brailletouch/Brailletouch/Electronica & firmware/celda braille con motor de celular/STL/assembly3 - PiezaBrailleParaMotores17-1.STL

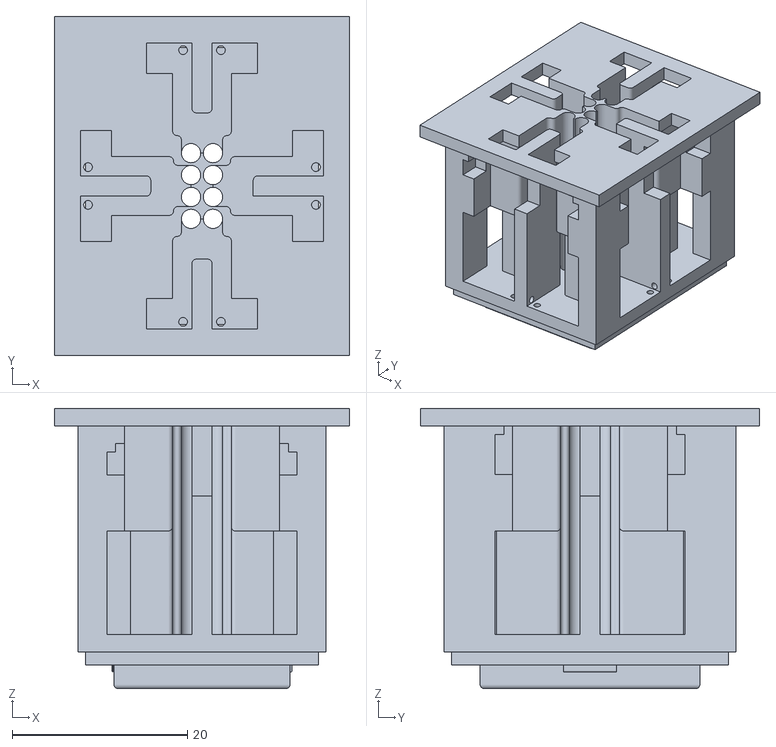
[picture p14: CAD file, 2024-08-29]
Electronica & firmware/celda braille con motor de celular/STL/assembly3 - PiezaBrailleParaMotores17-1.STL
33.7 x 38.7 x 32.0
