brailletouch/Brailletouch/Electronica & firmware/3d files/fcstd/celda completa.FCStd

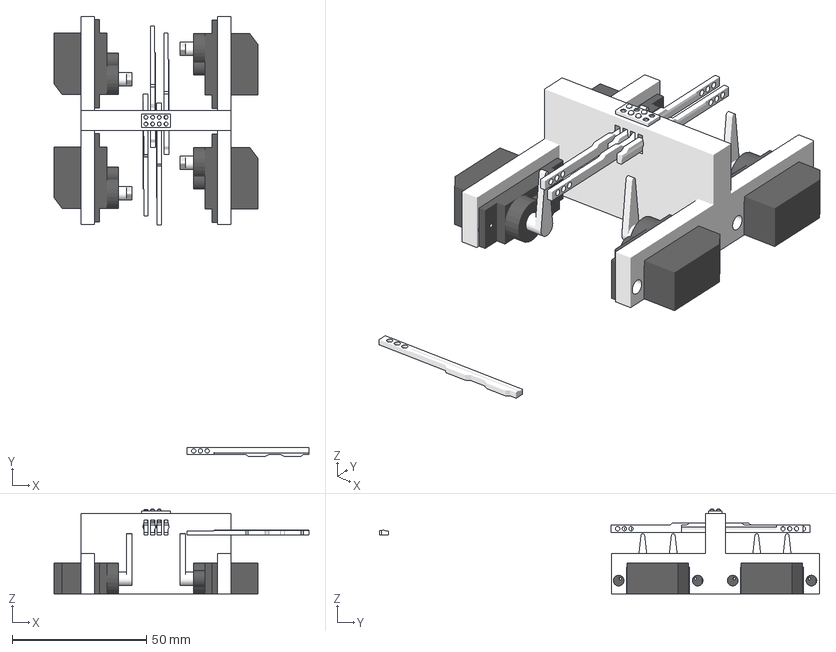
[picture p15: CAD file, 2021-12-04]
Electronica & firmware/3d files/fcstd/celda completa.FCStd
94.9 x 163.9 x 31.7 mm
