brailletouch/Brailletouch/Electronica & firmware/3d files/stl/barilla.stl

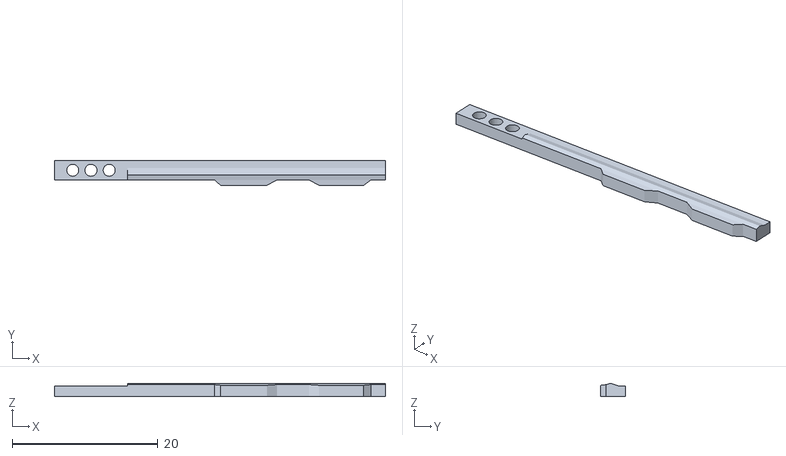
[picture p16: CAD file, 2021-12-04]
Electronica & firmware/3d files/stl/barilla.stl
45.4 x 3.40 x 1.85
