brailletouch/Brailletouch/Electronica & firmware/celda braille con motor de celular/SLDPRT/Pinizquierdo14.SLDPRT

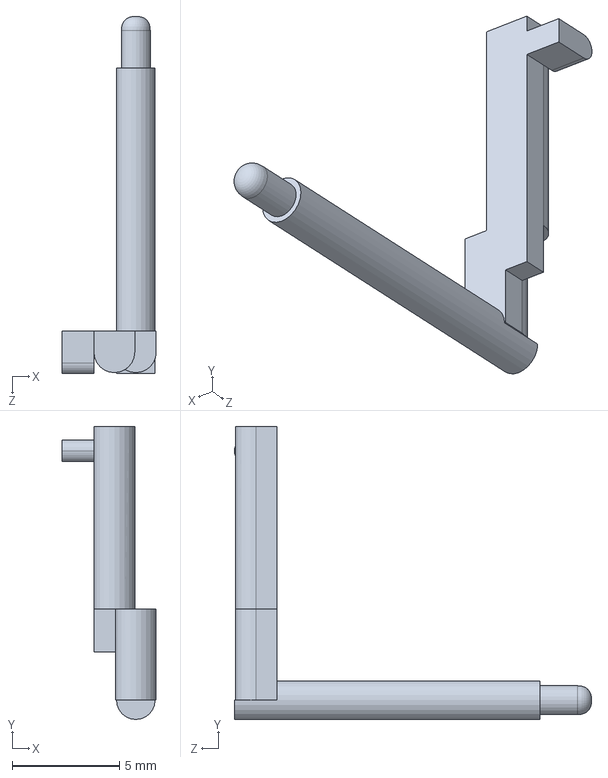
[picture p17: CAD file, 2024-08-17]
Electronica & firmware/celda braille con motor de celular/SLDPRT/Pinizquierdo14.SLDPRT
4.40 x 13.6 x 16.6 mm
