brailletouch/Brailletouch/Electronica & firmware/3d files/stl/celda braille.stl

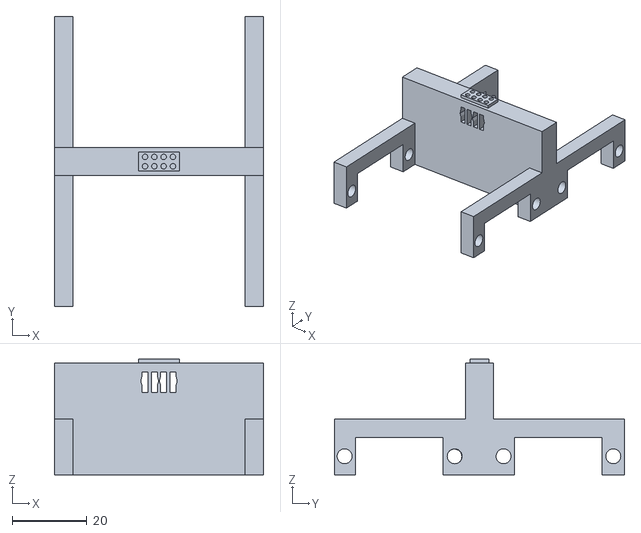
[picture p18: CAD file, 2021-12-04]
Electronica & firmware/3d files/stl/celda braille.stl
55.9 x 77.5 x 31.0
