brailletouch/Brailletouch/Electronica & firmware/celda braille con motor de celular/SLDPRT/TAPA_14.SLDPRT

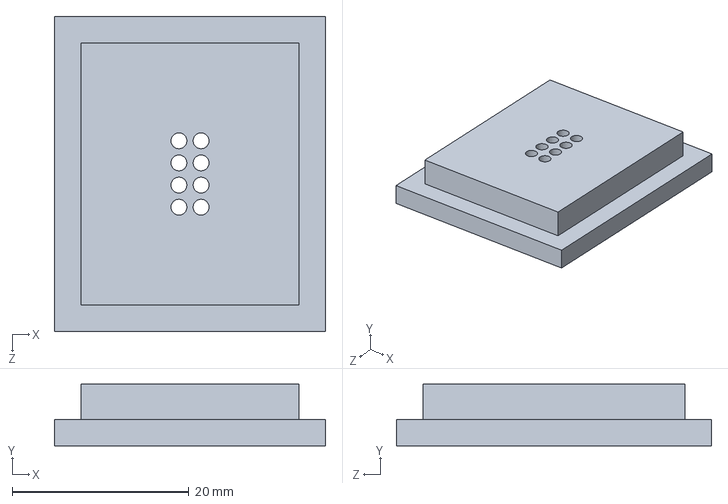
[picture p19: CAD file, 2024-08-17]
Electronica & firmware/celda braille con motor de celular/SLDPRT/TAPA_14.SLDPRT
30.6 x 7.00 x 35.7 mm
