brailletouch/Brailletouch/Electronica & firmware/3d files/stl/punto braille.stl

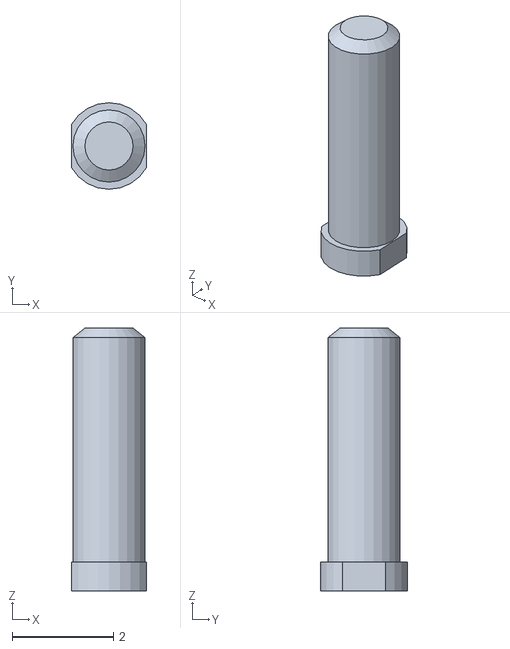
[picture p20: CAD file, 2021-12-04]
Electronica & firmware/3d files/stl/punto braille.stl
1.48 x 1.71 x 5.19
