brailletouch/Brailletouch/Electronica & firmware/celda braille con motor de celular/SLDPRT/PiezaBrailleParaMotores14.SLDPRT

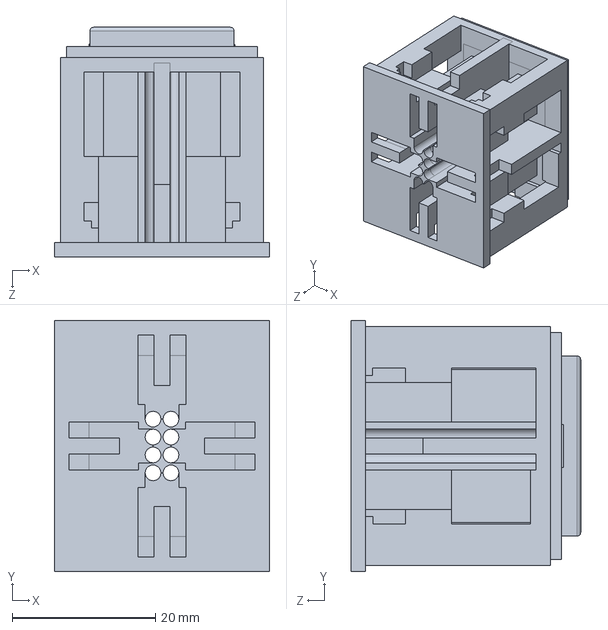
[picture p21: CAD file, 2024-08-17]
Electronica & firmware/celda braille con motor de celular/SLDPRT/PiezaBrailleParaMotores14.SLDPRT
30.0 x 35.0 x 32.0 mm
