brailletouch/Brailletouch/Electronica & firmware/celda braille con motor de celular/SLDPRT/CAPUCHAMOTOR14.SLDPRT

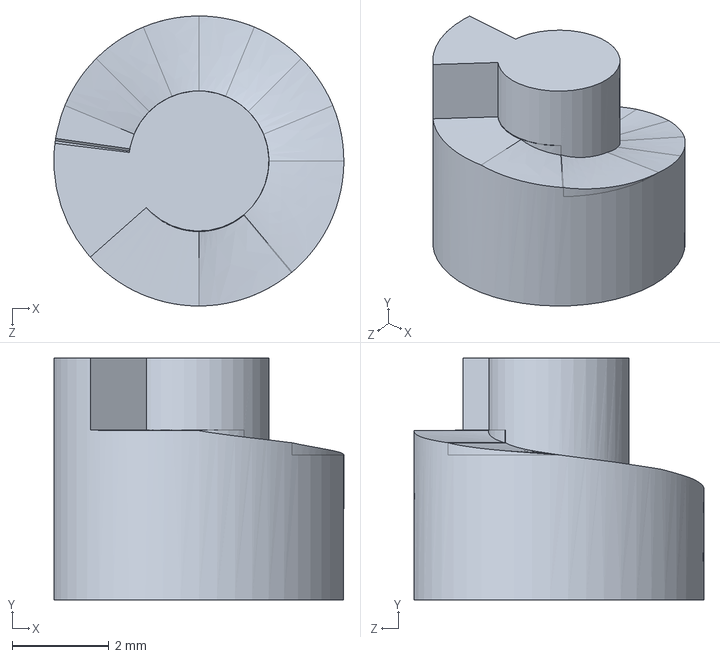
[picture p22: CAD file, 2024-08-17]
Electronica & firmware/celda braille con motor de celular/SLDPRT/CAPUCHAMOTOR14.SLDPRT
5.99 x 5.00 x 6.00 mm
