brailletouch/Brailletouch/Electronica & firmware/celda braille con motor de celular/image/assembly5.PNG

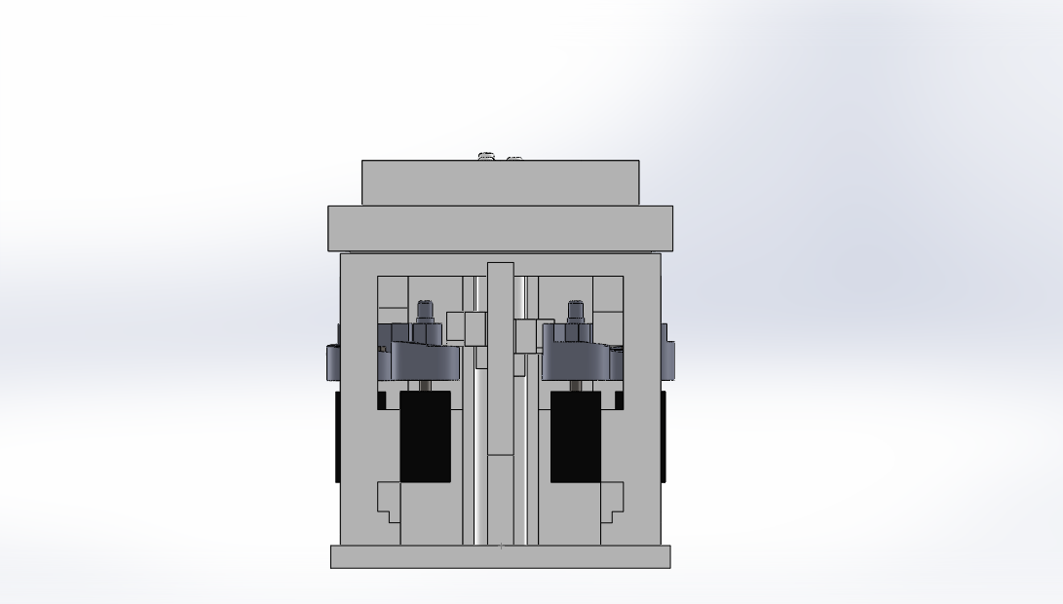
Electronica & firmware/celda braille con motor de celular/image/assembly5.PNG
