brailletouch/Brailletouch/Electronica & firmware/celda braille con motor de celular/image/assembly7.PNG

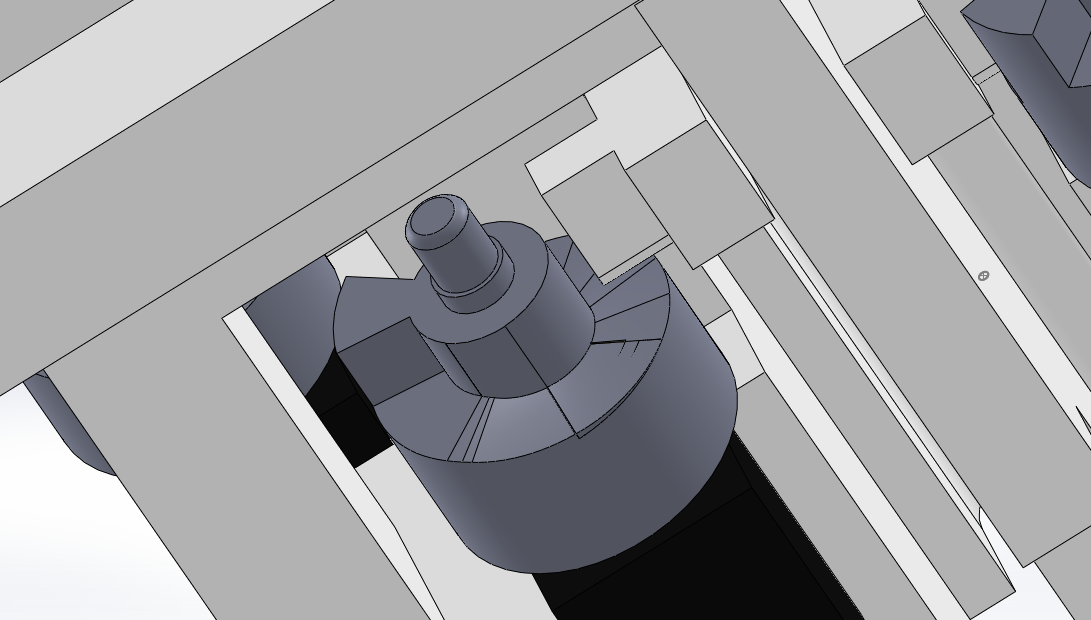
Electronica & firmware/celda braille con motor de celular/image/assembly7.PNG
