brailletouch/Brailletouch/Electronica & firmware/celda braille con motor de celular/image/assembly8.PNG

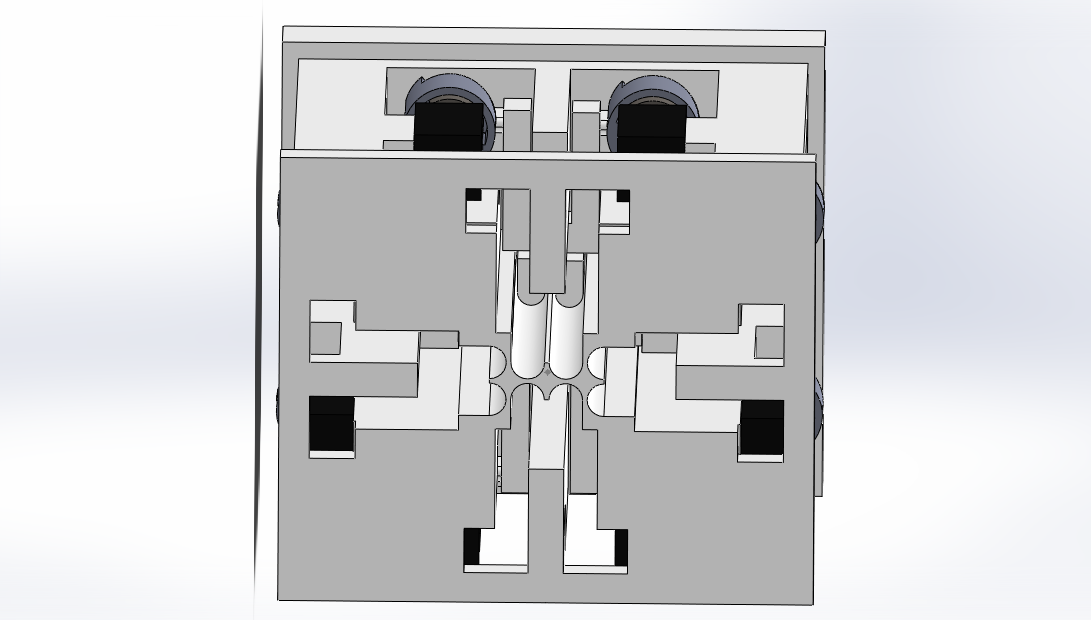
Electronica & firmware/celda braille con motor de celular/image/assembly8.PNG
