brailletouch/Brailletouch/Electronica & firmware/celda braille con motor de celular/image/assembly9.PNG

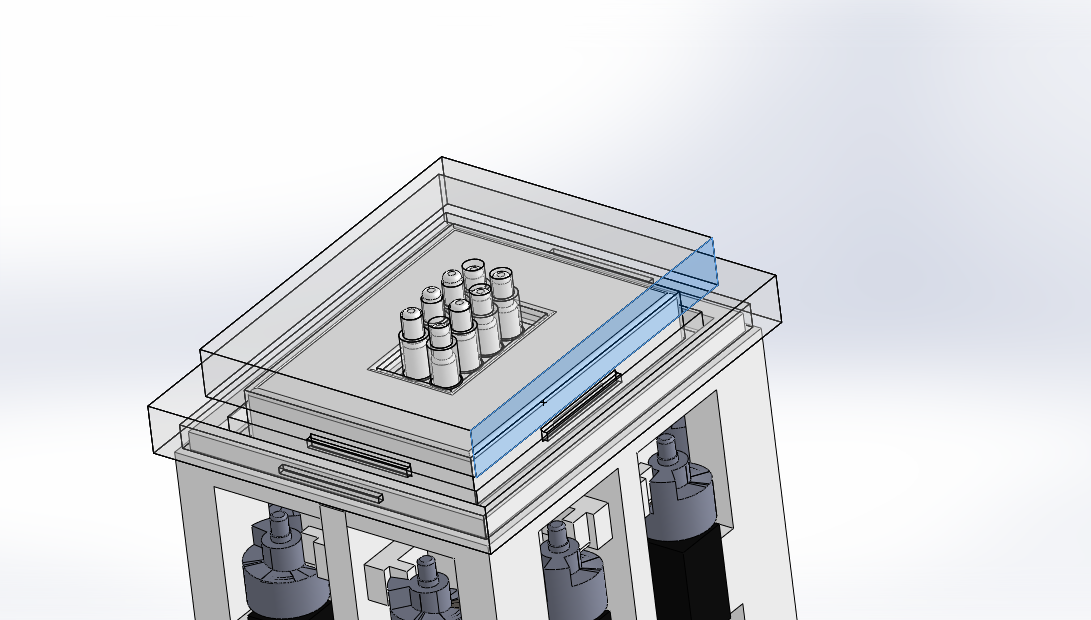
Electronica & firmware/celda braille con motor de celular/image/assembly9.PNG
