brailletouch/Brailletouch/Electronica & firmware/celda braille con motor de celular/image/assembly12.PNG

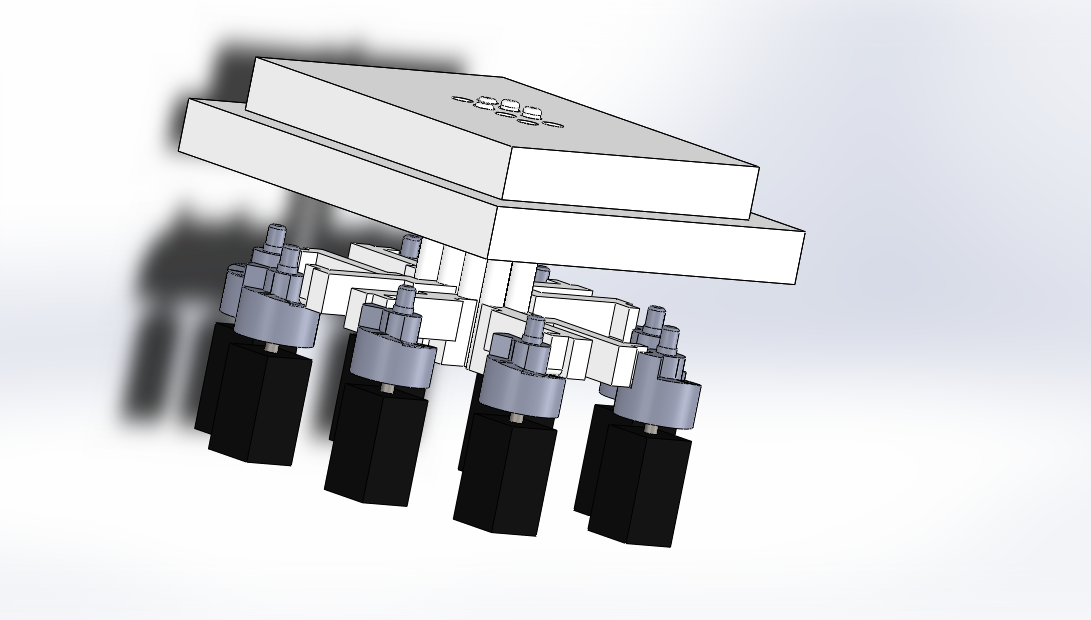
Electronica & firmware/celda braille con motor de celular/image/assembly12.PNG
