brailletouch/Brailletouch/Electronica & firmware/celda braille con motor de celular/image/assembly14.PNG

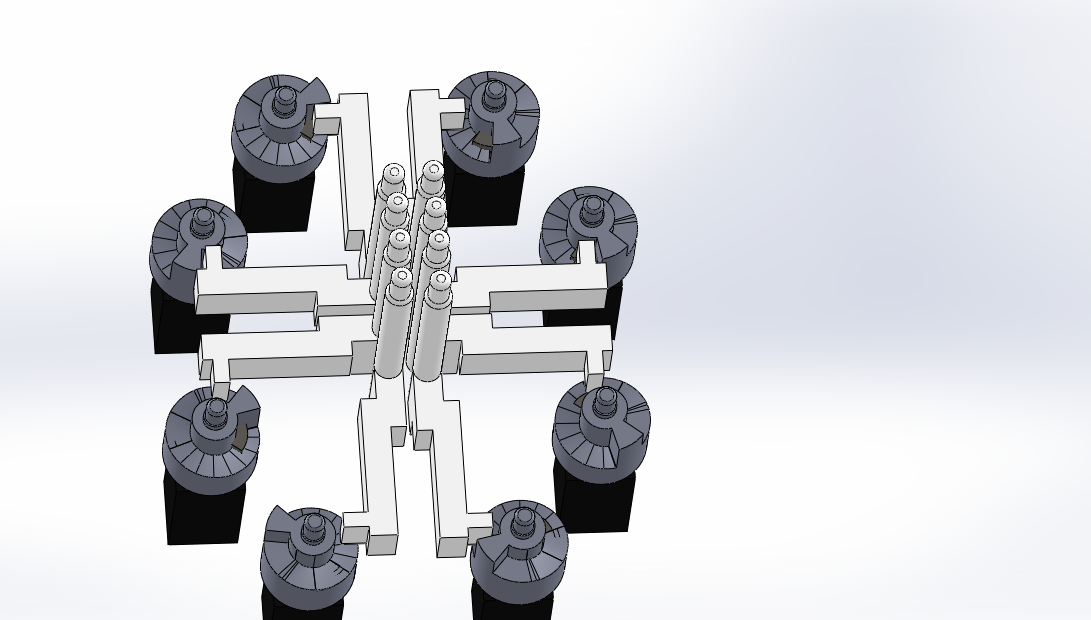
Electronica & firmware/celda braille con motor de celular/image/assembly14.PNG
