brailletouch/Brailletouch/Electronica & firmware/celda braille con motor de celular/image/assembly19.PNG

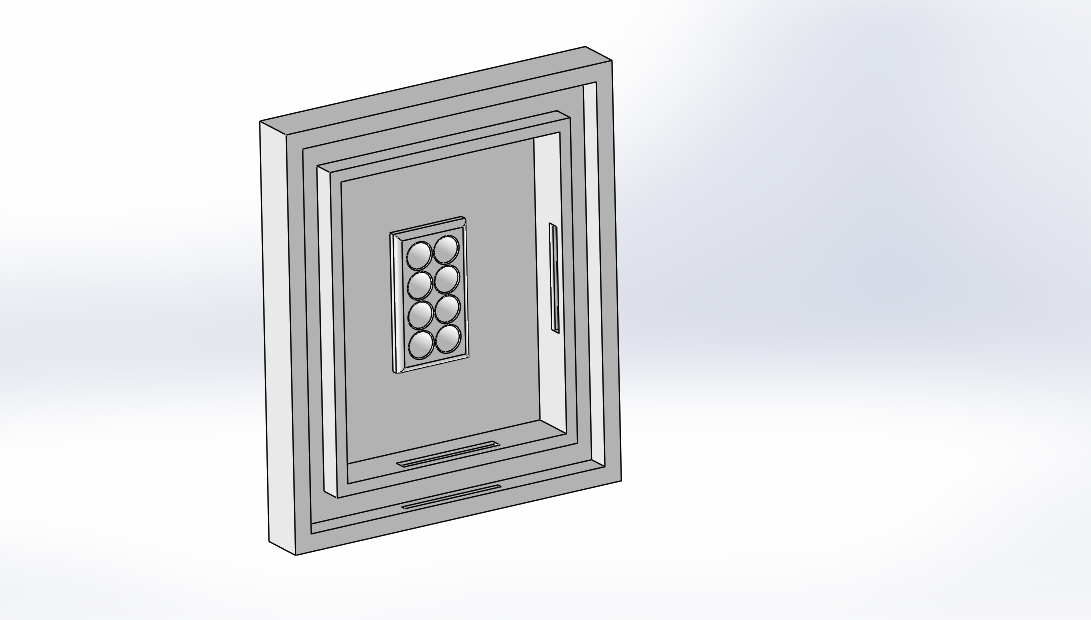
Electronica & firmware/celda braille con motor de celular/image/assembly19.PNG
